jpcf/Temperature_Measurement_Station_PIC16F1825/include/lib_LCD_Nokia5110.c

/*
Authors: José Pedro Fonseca, 2015
University of Porto, Portugal
*/


#include "lib_LCD_Nokia5110.h"
#include "PIC16F1825_configs.h"

/* The Font Matrix */
/*unsigned char ASCII[][2] = {0x00, 0x00}; */
const unsigned char ASCII[][6] = {
   {0x00, 0x00, 0x00, 0x00, 0x00, 0x00} /* 20   */  
  ,{0x00, 0x00, 0x5f, 0x00, 0x00, 0x00} /* 21 ! */
  ,{0x00, 0x07, 0x00, 0x07, 0x00, 0x00} /* 22 " */
  ,{0x14, 0x7f, 0x14, 0x7f, 0x14, 0x00} /* 23 # */
  ,{0x24, 0x2a, 0x7f, 0x2a, 0x12, 0x00} /* 24 $ */
  ,{0x23, 0x13, 0x08, 0x64, 0x62, 0x00} /* 25 % */
  ,{0x36, 0x49, 0x55, 0x22, 0x50, 0x00} /* 26 & */
  ,{0x00, 0x05, 0x03, 0x00, 0x00, 0x00} /* 27 ' */
  ,{0x00, 0x1c, 0x22, 0x41, 0x00, 0x00} /* 28 ( */
  ,{0x00, 0x41, 0x22, 0x1c, 0x00, 0x00} /* 29 ) */
  ,{0x14, 0x08, 0x3e, 0x08, 0x14, 0x00} /* 2a * */
  ,{0x08, 0x08, 0x3e, 0x08, 0x08, 0x00} /* 2b + */
  ,{0x00, 0x50, 0x30, 0x00, 0x00, 0x00} /* 2c , */
  ,{0x08, 0x08, 0x08, 0x08, 0x08, 0x00} /* 2d - */
  ,{0x00, 0x60, 0x60, 0x00, 0x00, 0x00} /* 2e . */
  ,{0x20, 0x10, 0x08, 0x04, 0x02, 0x00} /* 2f / */
  ,{0x3e, 0x51, 0x49, 0x45, 0x3e, 0x00} /* 30 0 */
  ,{0x00, 0x42, 0x7f, 0x40, 0x00, 0x00} /* 31 1 */
  ,{0x42, 0x61, 0x51, 0x49, 0x46, 0x00} /* 32 '\' */
  ,{0x21, 0x41, 0x45, 0x4b, 0x31, 0x00} /* 33 3 */
  ,{0x18, 0x14, 0x12, 0x7f, 0x10, 0x00} /* 34 4 */
  ,{0x27, 0x45, 0x45, 0x45, 0x39, 0x00} /* 35 5 */
  ,{0x3c, 0x4a, 0x49, 0x49, 0x30, 0x00} /* 36 6 */
  ,{0x01, 0x71, 0x09, 0x05, 0x03, 0x00} /* 37 7 */
  ,{0x36, 0x49, 0x49, 0x49, 0x36, 0x00} /* 38 8 */
  ,{0x06, 0x49, 0x49, 0x29, 0x1e, 0x00} /* 39 9 */
  ,{0x00, 0x36, 0x36, 0x00, 0x00, 0x00} /* 3a : */
  ,{0x00, 0x56, 0x36, 0x00, 0x00, 0x00} /* 3b ; */
  ,{0x08, 0x14, 0x22, 0x41, 0x00, 0x00} /* 3c < */
  ,{0x14, 0x14, 0x14, 0x14, 0x14, 0x00} /* 3d = */
  ,{0x00, 0x41, 0x22, 0x14, 0x08, 0x00} /* 3e > */
  ,{0x02, 0x01, 0x51, 0x09, 0x06, 0x00} /* 3f ? */
  ,{0x32, 0x49, 0x79, 0x41, 0x3e, 0x00} /* 40 @ */
  ,{0x7e, 0x11, 0x11, 0x11, 0x7e, 0x00} /* 41 A */
  ,{0x7f, 0x49, 0x49, 0x49, 0x36, 0x00} /* 42 B */
  ,{0x3e, 0x41, 0x41, 0x41, 0x22, 0x00} /* 43 C */
  ,{0x7f, 0x41, 0x41, 0x22, 0x1c, 0x00} /* 44 D */
  ,{0x7f, 0x49, 0x49, 0x49, 0x41, 0x00} /* 45 E */
  ,{0x7f, 0x09, 0x09, 0x09, 0x01, 0x00} /* 46 F */
  ,{0x3e, 0x41, 0x49, 0x49, 0x7a, 0x00} /* 47 G */
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
  ,{0x78, 0x46, 0x41, 0x46, 0x78, 0x00} /* 7f DEL */
};


void initLCD() {
    /* Some initial configs on port C */
    ANSELC &= 0x00; /* All bits on port C are set to Digital I/O's */
    TRISC  &= 0x00; /* All bits on Port C are set to Outputs */
    APFCON0 |= (1<<5); /* Don't use special features on Pin RC3 */
    APFCON1 |= (1<<2); /* Don't use special features on Pin RC3 */
    
    LATC = 0x00;
    
    /* All pins are initialy idle (HIGH), except for DIN */
    DC    = 1;
    SCE   = 1;
    RST   = 1;
    DIN   = 0;
    SCK   = 0;
    
    /* Initial reset to the device */
    __delay_ms(300);
    RST = 0;
    __delay_ms(300);
    RST = 1;
}

void configLCD() {
    unsigned char buf;
    buf = 0x21;
    sendByteLCD(&buf, 0);
    buf = 0xC0; /* Set the Operation Voltage to a good value */
    sendByteLCD(&buf, 0);
    buf = 0x07; /* Set the TempCoef to 4 */
    sendByteLCD(&buf, 0);
    buf = 0x13; /* Set Bias bits BSx. This way we get Mux of 1:48 */
    sendByteLCD(&buf, 0);
    buf = 0x20; /* Normal set of controls */
    sendByteLCD(&buf, 0);
    buf = 0x08; /* Clears the screen */
    sendByteLCD(&buf, 0);
    buf = 0x0C; /* Normal Display Mode */
    sendByteLCD(&buf, 0);
}

void sendByteLCD(unsigned char* buf, unsigned char dataCommand) {
    DC  = dataCommand;
    SCK = 0;
    __delay_us(1);
    SCE = 0;
    __delay_us(1);
    
    for(int i=0; i < 8; i++) {
        SCK = 0; /* Clock goes idle */
        
        /* Since we send the MSB first, we mask bit 8 and we send its logical value */
        (*buf) & 0b10000000 ? DIN = 1 : DIN = 0;  
        
        /* Rising Edge of the Clock */
        __delay_us(1);
        SCK = 1;
        __delay_us(1);
        
        /* We shift the next bit */
        (*buf) = ((*buf)<<1);
    }
    SCK = 0;
    SCE = 1;
}

void send_N_ByteLCD(unsigned char* buf, unsigned char dataCommand, int numBytes) {
    unsigned char tempByte = 0;
    
    DC  = dataCommand;
    SCK = 0;
    __delay_us(1);
    SCE = 0;
    __delay_us(1);
    
    for(int n=0; n < numBytes; n++) {
        tempByte = *(buf+n);
        for(int i=0; i < 8; i++) {
            SCK = 0; /* Clock goes idle */

            /* Since we send the MSB first, we mask bit 8 and we send its logical value */
            tempByte & 0b10000000 ? DIN = 1 : DIN = 0;  

            /* Rising Edge of the Clock */
            __delay_us(1);
            SCK = 1;
            __delay_us(1);

            /* We shift the next bit */
            tempByte = (tempByte<<1);
        }
    }
    SCK = 0;  
    SCE = 1;

}

void gotoXY(uint8_t X, uint8_t Y) {
    unsigned char buf = 0x40 + Y;
    sendByteLCD(&buf, 0);
    buf = 0x80 + X;
    sendByteLCD(&buf, 0);
}

void clearLCD(LCDcursor* cursor) {
    unsigned char buf = 0x00;
    
    for(int i=0; i<6; i++) {
        for(int j=0; j < 84; j++) {
            sendByteLCD(&buf, 1);
        }
    }
    /* Updates the screen cursor position */
    cursor->xPos = 0;
    cursor->yPos = 0;
}

void printCharLCD(char c) {
    send_N_ByteLCD(ASCII[c - 0x20], 1, 6);
}

void printlnLCD(char* str, uint8_t numBytes, uint8_t alignment, LCDcursor* cursor) {
    
    if (numBytes > 14 )
         numBytes = 14; /*Truncates string if it is longer than the screensize */

    /* This means it is left aligned */
    if (1 == alignment) {
        for(int i=0; i < numBytes; i++) {
            send_N_ByteLCD(ASCII[str[i] - 0x20], 1, 6);    
        }
    } else if(2 == alignment) {
        /* Moves the cursor to the correct position */
        gotoXY( 6*(14 - numBytes)/2, cursor->yPos % 6);
        
        /* Prints the actual string */
        for(int i=0; i < numBytes; i++) {
            send_N_ByteLCD(ASCII[str[i] - 0x20], 1, 6);
        }
    }
    /*Moves to the next line */
    gotoXY(0, (cursor->yPos + 1) % 6);
    cursor->yPos += 1;
}

void printImageLCD(char* imageStr) {
    gotoXY(0,0);
    send_N_ByteLCD(imageStr, 1, 504);
}
